BoujeeEnjinia1701/floodgauge/cad/drawings/FLG-DWG-001.pdf

CONCEPT, NOT FOR FABRICATION | FloodGauge · github.com/BoujeeEnjinia1701/floodgauge

TOP VIEW
Scale 1:50; looking down (along -Z)

FRONT VIEW
Scale 1:50; looking along the street

RIGHT VIEW
Scale 1:50; looking at the right side (along -X)

DETAIL A: STREET HEAD, ARM AND CLAMPS
Scale 1:10; front view

SECTION B: CATCH BASIN, DRAIN HEAD AND TUBE
Scale 1:20; basin cut on the street axis

PRELIMINARY, NOT FOR FABRICATION

ROAD, Z = 0 (DATUM)

SIDEWALK

4,600 lens to road

3,400 node center

300

250

CURB FACE

715 arm
700 head to pole axis

400 clamps

2 RADAR HEAD D76

M8 THROUGH-BOLT, ANTI-ROTATION

POLE BRACKET PLATE ON 2 V-BLOCKS

3 ARM 40 x 40 x 1.6

KNEE BRACE 25 SQ, 45 DEG

300
330

1,240 mouth

ROAD Z = 0

5 TUBE 75 OD x 940

4 DRAIN HEAD

WATER ENTERS VIA SLOTS

ISOMETRIC VIEW
Kit on the existing pole; not to scale; seen from the front right and above, about 30 deg elevation

MAIN DIMENSIONS AND INTERFACES (MM)
Datum: road surface at the gauge point, Z = 0; curb 150 Radar lens 4,600 above road, 250 past curb face Street depth 0 to 600: range 4,600 to 4,000
FieldNode 150 x 90 x 200 on 60 pole, center 3,400 Arm 40 sq x 715 in cleats on a 3 x 100 x 450 plate Pole bracket on 2 V-blocks, band clamps 400 apart
Tube 75 OD, ID 69, 940 long, 40 slots 5 x 50
Drain reading 330 to 1,250 below road; probe 310
Pilot cable route: 3 hat covers 764 long, curb and sidewalk anchors; riser guard Marker bands 150 to 300 amber, 300 to 450 red
Lens height 2,500 to 5,000 per site, clearance rule (FLG-CAL-001 A7)
REV | DESCRIPTION | DATE | BY
P1 | Preliminary GA for TRL 3 (from cad/src/model.py) | 2026-09-25 | AC
P2 | DDR-002: lens 4.6 m, node 3.0 m, surface cable cover, anti-rotation bolt | 2026-09-25 | AC
P3 | Layout and labels tidied | 2026-09-25 | AC
P4 | DDR-003: constructable design; node at 3.4 m | 2026-10-01 | AC
P5 | Drain cable slack loop tied to tube clamp | 2026-10-02 | AC
FLOODGAUGE | github.com/BoujeeEnjinia1701/floodgauge

## General arrangement

DRAWING NO.
FLG-DWG-001

REV
P5

SHEET
1 of 1

SIZE

## ANSI B

SCALE
1:50

UNITS
mm
PROJECTION | DATE
2026-10-02

DRAWN
Amish Chadha

MATERIAL / NOTES
Aluminium arm, PVC tube, bought-in heads per bom/bom.csv; existing street shown for context. PRELIMINARY, NOT FOR FABRICATION
Licensed CERN-OHL-S-2.0 · Design Molecule Lab · designmolecule.com | Generated from cad/src; do not edit by hand
