BoujeeEnjinia1701/floodgauge/cad/drawings/FLG-DWG-110.pdf

BUILD PLAN SKETCH, PLAN NOT YET BUILT FloodGauge · github.com/BoujeeEnjinia1701/floodgauge

FRONT VIEW
Scale 1:5; looking at the front (along +Y)

TOP VIEW
Scale 1:5; looking down (along -Z)

RIGHT VIEW
Scale 1:5; looking at the right side (along -X)

90

2 435

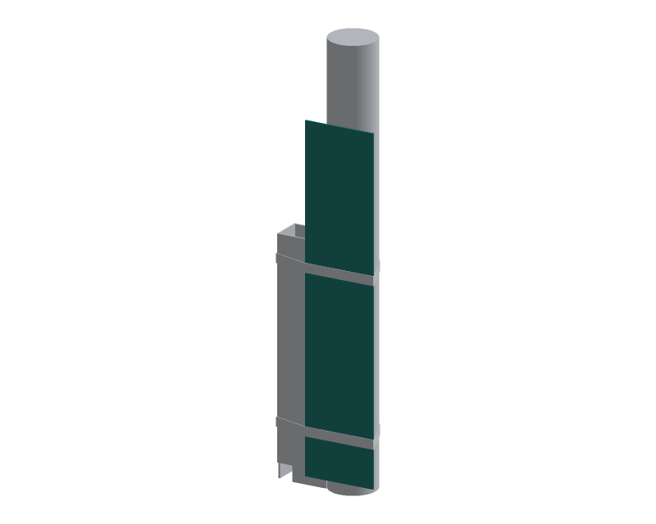
[picture p8: figure]

WHERE IT GOES
This part in colour, its neighbours in grey

HOW TO MAKE IT AND HOW IT FITS
Cut 90 x 435 mm from 2 mm aluminium; round the corners, deburr.
The bottom edge sits 165 mm above the road (15 mm above the sidewalk), so the sidewalk cover passes under it. Heights below are from the road.
Amber reflective film from the bottom edge up to 300 mm above the road (135 mm up the plate). Red film from 300 to 450 mm above the road
(135 to 285 mm up the plate). Leave the top 150 mm plain for a label. Mark a black line at 150 mm and 300 mm above the road (the alert depths) and number them.
No holes: two band clamps go round the pole, across the plate's face and round the riser guard, at 220 and 420 mm above the road. Check: film edges straight and level when the plate is held plumb.
REV | DESCRIPTION | DATE | BY
P1 | Making sketch for the prototype build plan | 2026-10-01 | AC
FLOODGAUGE | github.com/BoujeeEnjinia1701/floodgauge

## FloodGauge depth marker plate: making sketch

DRAWING NO.
FLG-DWG-110

REV
P1

SHEET
1 of 1

SIZE

## ANSI B

SCALE
1:5

UNITS
mm
PROJECTION | DATE
2026-10-01

DRAWN
Amish Chadha

MATERIAL / NOTES
Aluminium sheet 2 mm with reflective film
Licensed CERN-OHL-S-2.0 · Design Molecule Lab · designmolecule.com | Generated from cad/src; do not edit by hand
