BoujeeEnjinia1701/floodgauge/cad/drawings/FLG-DWG-111.pdf

BUILD PLAN SKETCH, PLAN NOT YET BUILT FloodGauge · github.com/BoujeeEnjinia1701/floodgauge

FRONT VIEW
Scale 1:5; looking at the front (along +Y)

TOP VIEW
Scale 1:5; looking down (along -Z)

RIGHT VIEW
Scale 1:5; looking at the right side (along -X)

40

65 300

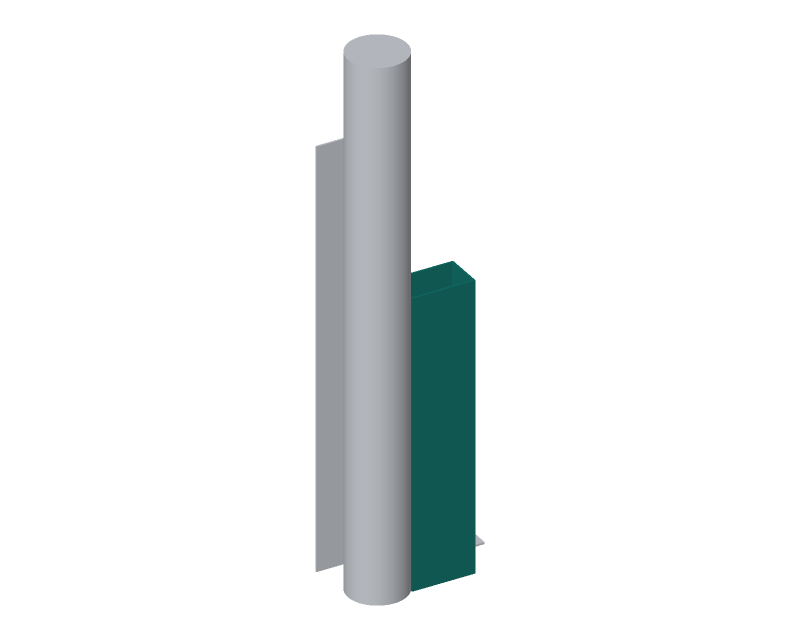
[picture p9: figure]

WHERE IT GOES
This part in colour, its neighbours in grey

HOW TO MAKE IT AND HOW IT FITS
Cut a blank 300 x 162 mm from 2 mm galvanized sheet.
Fold to a U: back 40 mm wide outside, two sides 65 mm deep. Fold in a sheet folder or over a hardwood block in the vice.
Cut a 20 x 20 mm notch at the foot of the side that faces the road, against the back: the cable comes out of the sidewalk cover here. File every edge smooth; paint the cut edges with zinc paint.
Fit: open side against the pole, the free edges of both sides bearing
on the pole; it stands on the sidewalk beside the pole, 300 mm tall.
The two marker band clamps go round it and hold it (pin-Torx security screws). Check: the free edges touch the pole along their whole length.
REV | DESCRIPTION | DATE | BY
P1 | Making sketch for the prototype build plan | 2026-10-01 | AC
FLOODGAUGE | github.com/BoujeeEnjinia1701/floodgauge

## FloodGauge riser guard: making sketch

DRAWING NO.
FLG-DWG-111

REV
P1

SHEET
1 of 1

SIZE

## ANSI B

SCALE
1:5

UNITS
mm
PROJECTION | DATE
2026-10-01

DRAWN
Amish Chadha

MATERIAL / NOTES
Galvanized steel sheet 2 mm
Licensed CERN-OHL-S-2.0 · Design Molecule Lab · designmolecule.com | Generated from cad/src; do not edit by hand
