BoujeeEnjinia1701/floodgauge/cad/drawings/FLG-DWG-114.pdf

BUILD PLAN SKETCH, PLAN NOT YET BUILT FloodGauge · github.com/BoujeeEnjinia1701/floodgauge

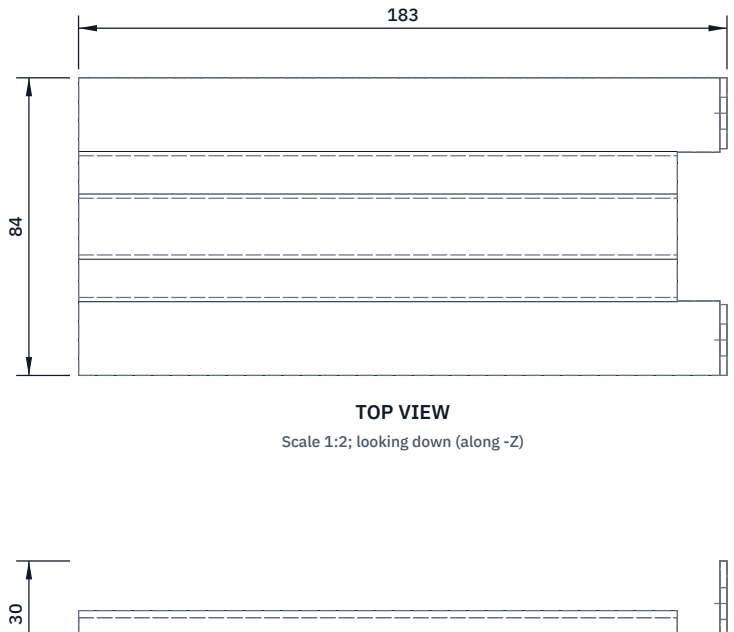
[picture p10: figure]
TOP VIEW; Scale 1:2; looking down (along -Z)

FRONT VIEW
Scale 1:2; looking at the front (along +Y)

RIGHT VIEW
Scale 1:2; looking at the right side (along -X)

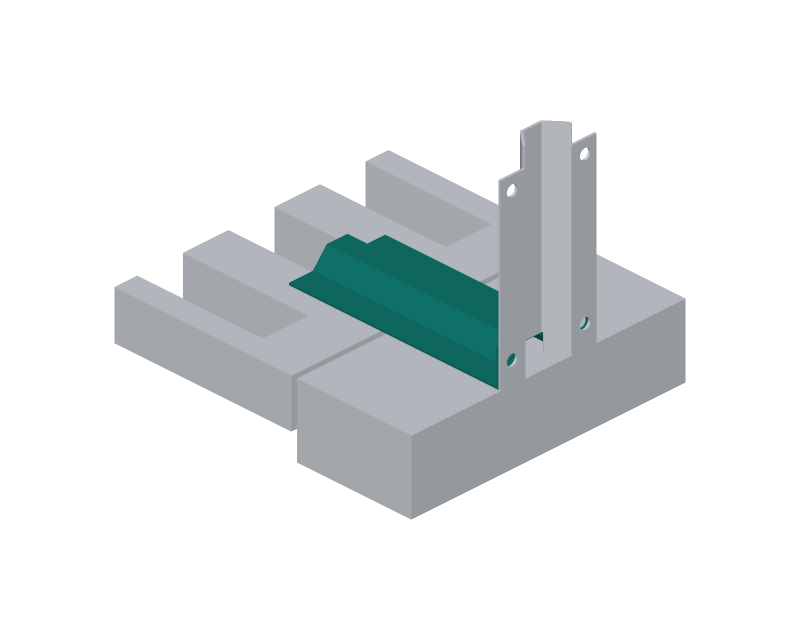
[picture p11: figure]

WHERE IT GOES
This part in colour, its neighbours in grey

HOW TO MAKE IT AND HOW IT FITS
Hat section: from 2 mm galvanized strip 84 mm wide, folded to two
22 mm flanges, two 45 degree sides and a 16 mm wide top, 16 mm high overall. Fold in a sheet folder; cut lengths with a grinder.
Paint the cut ends with zinc paint; file all edges smooth.
Cut 211 mm of hat section. At one end cut away the top and
sides for 42 mm, leaving the two flanges; fold the flanges up
90 degrees 30 mm from their ends to make the tabs (169 mm of raised part). Drill a 9 mm hole in each tab, 18 mm up, 32 mm from the centre line.
Fit: lies across the gutter strip and 80 mm onto the grate's border,
over the cable. The tabs go over the curb cover's flanges and
share its two lower anchors (security nuts). Nothing is fixed to the road. Check: lies flat with no rocking.
REV | DESCRIPTION | DATE | BY
P1 | Making sketch for the prototype build plan | 2026-10-01 | AC
FLOODGAUGE | github.com/BoujeeEnjinia1701/floodgauge

## FloodGauge gutter cover: making sketch

DRAWING NO.
FLG-DWG-114

REV
P1

SHEET
1 of 1

SIZE

## ANSI B

SCALE
1:2

UNITS
mm
PROJECTION | DATE
2026-10-01

DRAWN
Amish Chadha

MATERIAL / NOTES
Galvanized steel strip 2 mm
Licensed CERN-OHL-S-2.0 · Design Molecule Lab · designmolecule.com | Generated from cad/src; do not edit by hand
