BoujeeEnjinia1701/floodgauge/cad/drawings/FLG-DWG-115.pdf

BUILD PLAN SKETCH, PLAN NOT YET BUILT FloodGauge · github.com/BoujeeEnjinia1701/floodgauge

FRONT VIEW
Scale 1:2; looking at the front (along +Y)

TOP VIEW
Scale 1:2; looking down (along -Z)

RIGHT VIEW
Scale 1:2; looking at the right side (along -X)

16

84 166

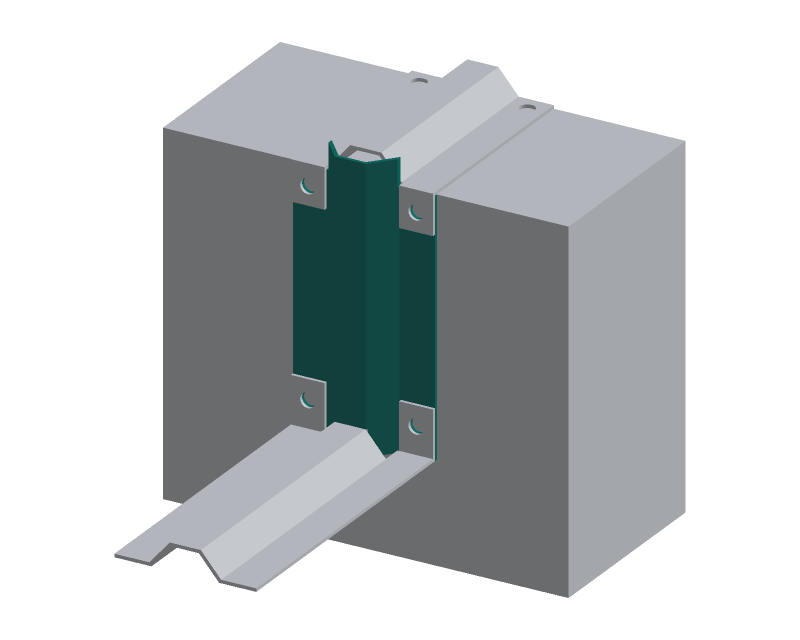
[picture p12: figure]

WHERE IT GOES
This part in colour, its neighbours in grey

HOW TO MAKE IT AND HOW IT FITS
Hat section: from 2 mm galvanized strip 84 mm wide, folded to two
22 mm flanges, two 45 degree sides and a 16 mm wide top, 16 mm high overall. Fold in a sheet folder; cut lengths with a grinder.
Paint the cut ends with zinc paint; file all edges smooth.
Length 166 mm of hat section. Cut both flanges off the top 16 mm (only the raised part rises above the sidewalk).
Cut a 20 x 16 mm notch in the raised face at the bottom end for the cable coming out of the gutter cover.
Four 9 mm holes in the flanges, 32 mm from the centre line, 18 and 139 mm up from the bottom end.
Fit: flanges flat on the curb face, standing on the road; four M8 masonry anchors, snake-eye security nuts, through it and the tabs. Check: the top of the raised part is 16 mm above the sidewalk.
REV | DESCRIPTION | DATE | BY
P1 | Making sketch for the prototype build plan | 2026-10-01 | AC
FLOODGAUGE | github.com/BoujeeEnjinia1701/floodgauge

## FloodGauge curb cover: making sketch

DRAWING NO.
FLG-DWG-115

REV
P1

SHEET
1 of 1

SIZE

## ANSI B

SCALE
1:2

UNITS
mm
PROJECTION | DATE
2026-10-01

DRAWN
Amish Chadha

MATERIAL / NOTES
Galvanized steel strip 2 mm
Licensed CERN-OHL-S-2.0 · Design Molecule Lab · designmolecule.com | Generated from cad/src; do not edit by hand
