BoujeeEnjinia1701/floodgauge/cad/drawings/FLG-DWG-116.pdf

BUILD PLAN SKETCH, PLAN NOT YET BUILT FloodGauge · github.com/BoujeeEnjinia1701/floodgauge

FRONT VIEW
Scale 1:5; looking at the front (along +Y)

TOP VIEW
Scale 1:5; looking down (along -Z)

RIGHT VIEW
Scale 1:5; looking at the right side (along -X)

433

84 38

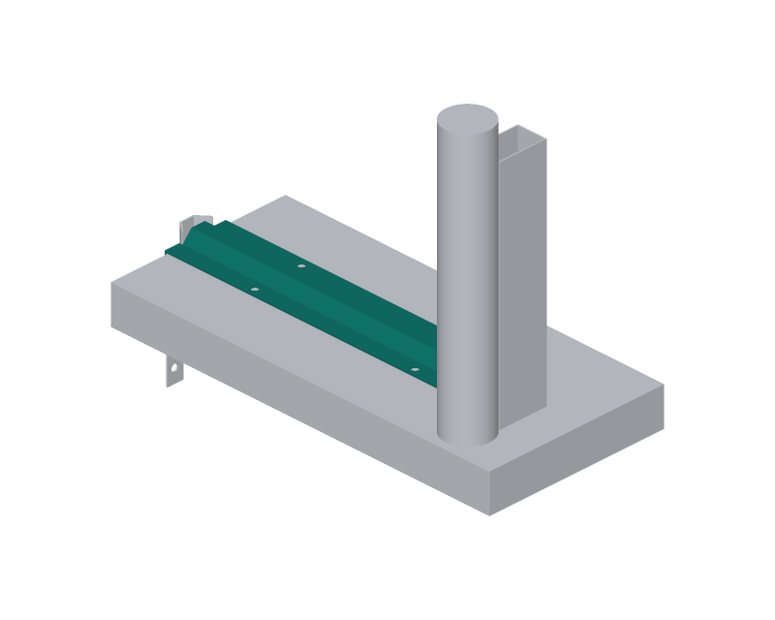
[picture p13: figure]

WHERE IT GOES
This part in colour, its neighbours in grey

HOW TO MAKE IT AND HOW IT FITS
Hat section: from 2 mm galvanized strip 84 mm wide, folded to two
22 mm flanges, two 45 degree sides and a 16 mm wide top, 16 mm high overall. Fold in a sheet folder; cut lengths with a grinder.
Paint the cut ends with zinc paint; file all edges smooth.
Cut 455 mm of hat section. At one end cut away the top and
sides for 26 mm, leaving the two flanges; fold the flanges down
90 degrees 22 mm from their ends to make the tabs (429 mm raised). Four 9 mm holes in the flanges, 32 mm from the centre line, 110 and 330 mm from the curb end; a 9 mm hole in each tab, 11 mm down. Grind a 45 degree bevel on the flange edges so it is not a trip edge. Fit: across the sidewalk from the curb edge to 1 mm short of the riser guard; four M8 anchors, security nuts; tabs share the curb cover's upper anchors. Paint it yellow or fit hazard tape.
Check: no edge stands more than 2 mm off the sidewalk.
REV | DESCRIPTION | DATE | BY
P1 | Making sketch for the prototype build plan | 2026-10-01 | AC
FLOODGAUGE | github.com/BoujeeEnjinia1701/floodgauge

## FloodGauge sidewalk cover: making sketch

DRAWING NO.
FLG-DWG-116

REV
P1

SHEET
1 of 1

SIZE

## ANSI B

SCALE
1:5

UNITS
mm
PROJECTION | DATE
2026-10-01

DRAWN
Amish Chadha

MATERIAL / NOTES
Galvanized steel strip 2 mm
Licensed CERN-OHL-S-2.0 · Design Molecule Lab · designmolecule.com | Generated from cad/src; do not edit by hand
