BoujeeEnjinia1701/floodgauge/cad/drawings/FLG-DWG-101.pdf

BUILD PLAN SKETCH, PLAN NOT YET BUILT FloodGauge · github.com/BoujeeEnjinia1701/floodgauge

FRONT VIEW
Scale 1:5; looking at the front (along +Y)

TOP VIEW
Scale 1:5; looking down (along -Z)

RIGHT VIEW
Scale 1:5; looking at the right side (along -X)

100

3 450

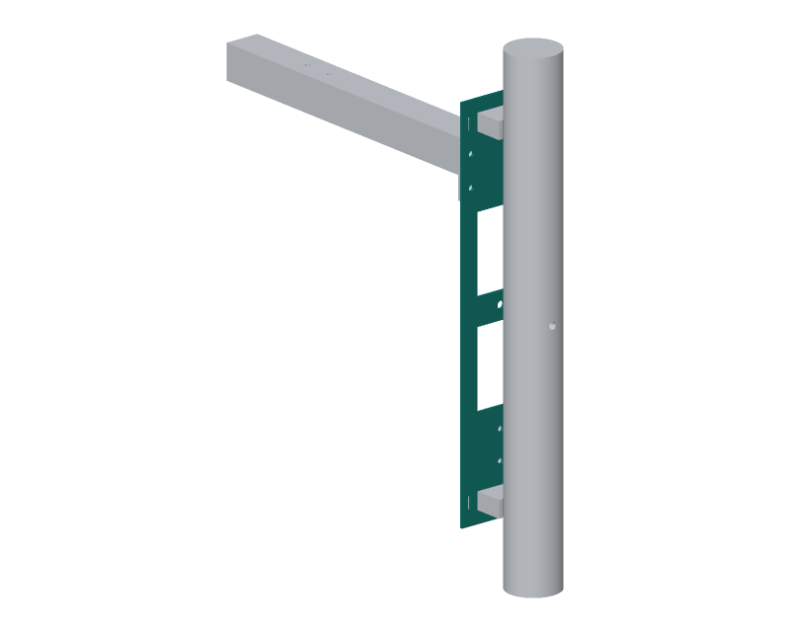
[picture p53: figure]

WHERE IT GOES
This part in colour, its neighbours in grey

HOW TO MAKE IT AND HOW IT FITS
Blank 100 x 450 mm, 3 mm aluminium. Front view is the face toward the road. Heights up from the bottom edge; sideways from the centre line.
Band slots 3 x 15 mm at 40 mm each side, centred 25 and 425 mm up:
chain drill 3 mm and file square. The band clamps pass through these. V-block screws 4.5 mm at 18 mm each side, 25 and 425 mm up; countersink from the front so the M4 heads sit flush under the band.
Brace clip bolts 6.6 mm on the centre line, 60 and 94 mm up.
Through-bolt hole 8.5 mm on the centre line, 225 mm up.
Arm cleat bolts 6.6 mm at 38 mm each side, 357 and 393 mm up.
Two windows 60 x 90 mm, centred 164 and 285 mm up (saves weight): drill 10 mm in the corners, cut between with a jigsaw, file straight. Deburr every hole and edge; round the corners to about 2 mm.
Check: lay the V-blocks, cleats and clip on it; every hole lines up.
REV | DESCRIPTION | DATE | BY
P1 | Making sketch for the prototype build plan | 2026-10-01 | AC
FLOODGAUGE | github.com/BoujeeEnjinia1701/floodgauge

## FloodGauge pole bracket plate: making sketch

DRAWING NO.
FLG-DWG-101

REV
P1

SHEET
1 of 1

SIZE

## ANSI B

SCALE
1:5

UNITS
mm
PROJECTION | DATE
2026-10-01

DRAWN
Amish Chadha

MATERIAL / NOTES
Aluminium sheet 3 mm, 5052 or 6061 class
Licensed CERN-OHL-S-2.0 · Design Molecule Lab · designmolecule.com | Generated from cad/src; do not edit by hand
