BoujeeEnjinia1701/floodgauge/cad/drawings/FLG-DWG-102.pdf

BUILD PLAN SKETCH, PLAN NOT YET BUILT FloodGauge · github.com/BoujeeEnjinia1701/floodgauge

FRONT VIEW
Scale 1:1; looking at the front (along +Y)

TOP VIEW
Scale 1:1; looking down (along -Z)

RIGHT VIEW
Scale 1:1; looking at the right side (along -X)

33

60 20

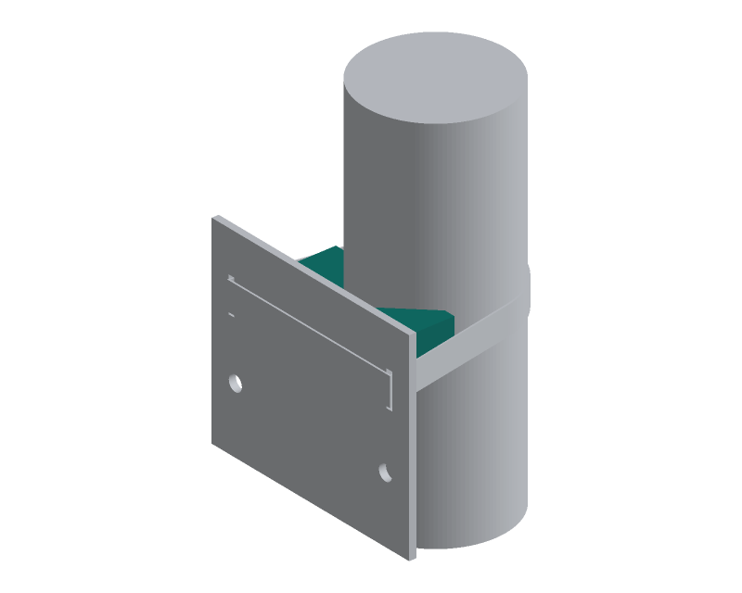
[picture p54: figure]

WHERE IT GOES
This part in colour, its neighbours in grey

HOW TO MAKE IT AND HOW IT FITS
Make two; the same block as FieldNode's (FND-DWG-102). Saw a 20 mm slice off 60 x 40 mm bar; saw and file to 60 wide x 33 deep x 20 tall.
The flat back goes on the bracket plate.
Scribe a 90 degree V on both 60 x 33 faces with a 45 degree square: 50.4 mm wide at the front face, point 7.8 mm from the back face. Saw just inside the lines, file to them; keep the V faces flat.
Break the V's front edges 0.5 mm so they cannot score the pole. Drill 3.3 mm 14 deep and tap M4 12 deep in the back face, at 18 mm each side of centre, half way up (10 mm).
Fit: two M4 countersunk screws from the front of the plate. The 60 mm pole touches both V faces 29 mm from the plate; 40 to 71 mm poles seat. Check: on a 60 mm tube the block must not rock.
REV | DESCRIPTION | DATE | BY
P1 | Making sketch for the prototype build plan | 2026-10-01 | AC
FLOODGAUGE | github.com/BoujeeEnjinia1701/floodgauge

## FloodGauge V-block (make 2): making sketch

DRAWING NO.
FLG-DWG-102

REV
P1

SHEET
1 of 1

SIZE

## ANSI B

SCALE
1:1

UNITS
mm
PROJECTION | DATE
2026-10-01

DRAWN
Amish Chadha

MATERIAL / NOTES
Aluminium flat bar 60 x 40 mm, 6082 or 6061
Licensed CERN-OHL-S-2.0 · Design Molecule Lab · designmolecule.com | Generated from cad/src; do not edit by hand
