BoujeeEnjinia1701/floodgauge/cad/drawings/FLG-DWG-103.pdf

BUILD PLAN SKETCH, PLAN NOT YET BUILT FloodGauge · github.com/BoujeeEnjinia1701/floodgauge

FRONT VIEW
Scale 1:1; looking at the front (along +Y)

TOP VIEW
Scale 1:1; looking down (along -Z)

RIGHT VIEW
Scale 1:1; looking at the right side (along -X)

30

30 60

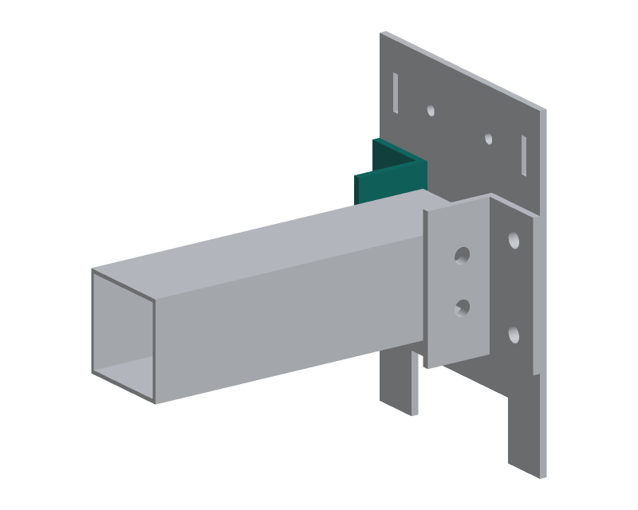
[picture p55: figure]

WHERE IT GOES
This part in colour, its neighbours in grey

HOW TO MAKE IT AND HOW IT FITS
Cut two 60 mm lengths of 30 x 30 x 3 angle; square and deburr the ends. Plate leg (goes flat on the bracket plate): two 6.6 mm holes, 12 mm
in from its free edge, 12 and 48 mm up from the bottom end.
Arm leg (lies along the arm's side): two 6.6 mm holes, 15 mm out from the face that sits on the plate, 20 and 40 mm up from the bottom end. Left and right cleats are mirror images: drill them clamped as a pair. Fit: plate legs flat on the plate front, 345 to 405 mm up it, arm legs 40 mm apart; two M6 bolts each through the plate (nuts behind);
the arm slides between the arm legs and two M6 bolts with crush sleeves pass through cleat, arm and cleat.
Check: both cleats square to the plate, arm legs parallel, 40 mm apart.
REV | DESCRIPTION | DATE | BY
P1 | Making sketch for the prototype build plan | 2026-10-01 | AC
FLOODGAUGE | github.com/BoujeeEnjinia1701/floodgauge

## FloodGauge arm cleat (make 2, a left and a right): making sketch

DRAWING NO.
FLG-DWG-103

REV
P1

SHEET
1 of 1

SIZE

## ANSI B

SCALE
1:1

UNITS
mm
PROJECTION | DATE
2026-10-01

DRAWN
Amish Chadha

MATERIAL / NOTES
Aluminium equal angle 30 x 30 x 3 mm
Licensed CERN-OHL-S-2.0 · Design Molecule Lab · designmolecule.com | Generated from cad/src; do not edit by hand
