BoujeeEnjinia1701/floodgauge/cad/drawings/FLG-DWG-104.pdf

BUILD PLAN SKETCH, PLAN NOT YET BUILT FloodGauge · github.com/BoujeeEnjinia1701/floodgauge

FRONT VIEW
Scale 1:1; looking at the front (along +Y)

TOP VIEW
Scale 1:1; looking down (along -Z)

RIGHT VIEW
Scale 1:1; looking at the right side (along -X)

32

32 50

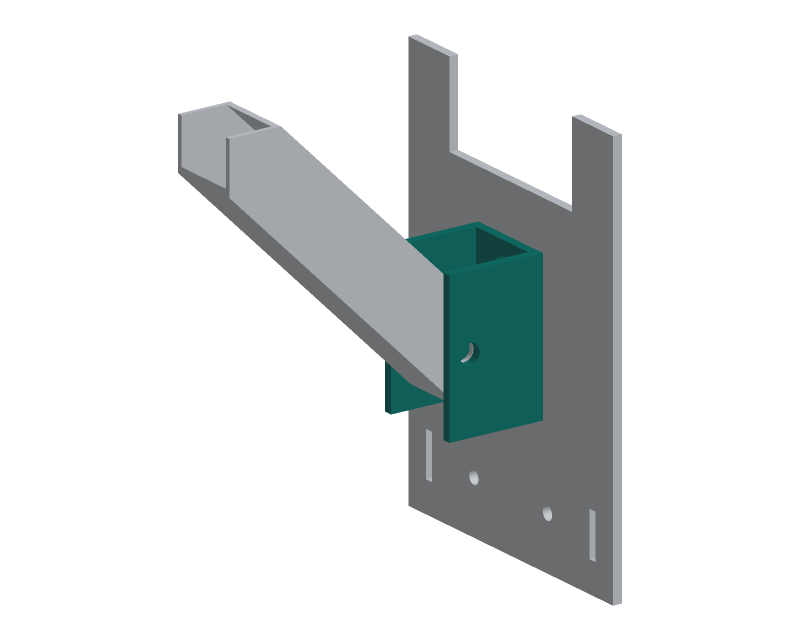
[picture p56: figure]

WHERE IT GOES
This part in colour, its neighbours in grey

HOW TO MAKE IT AND HOW IT FITS
Make two the same. Cut a 50 x 90 mm blank from 3 mm strip. Fold it to a U: base 31.5 mm wide outside, inside gap 25.5 mm,
ears 32 mm deep from the outside of the base. Fold in a vice over
a 25 mm steel block so the gap comes out right.
Base: two 6.6 mm holes on the centre line, 17 mm each side of the middle. Ears: one 6.6 mm hole through both, at mid-length, 25 mm out from
the outside of the base. Drill both ears in one pass after folding.
Fit: one clip under the arm, base up, ears hanging down (two M6 bolts
up through the arm, crush sleeves, nuts on top). The other on the bracket plate, ears forward (two M6 bolts, nuts behind the plate). The brace end sits between the ears on one M6 pin with a sleeve. Check: a 25 mm square tube slides between the ears without play.
REV | DESCRIPTION | DATE | BY
P1 | Making sketch for the prototype build plan | 2026-10-01 | AC
FLOODGAUGE | github.com/BoujeeEnjinia1701/floodgauge

## FloodGauge brace clip (make 2): making sketch

DRAWING NO.
FLG-DWG-104

REV
P1

SHEET
1 of 1

SIZE

## ANSI B

SCALE
1:1

UNITS
mm
PROJECTION | DATE
2026-10-01

DRAWN
Amish Chadha

MATERIAL / NOTES
Aluminium strip 3 mm x 50 mm, 5052 class
Licensed CERN-OHL-S-2.0 · Design Molecule Lab · designmolecule.com | Generated from cad/src; do not edit by hand
