BoujeeEnjinia1701/floodgauge/cad/drawings/FLG-DWG-105.pdf

BUILD PLAN SKETCH, PLAN NOT YET BUILT FloodGauge · github.com/BoujeeEnjinia1701/floodgauge

FRONT VIEW
Scale 1:5; looking at the front (along +Y)

TOP VIEW
Scale 1:5; looking down (along -Z)

RIGHT VIEW
Scale 1:5; looking at the right side (along -X)

715

40 40

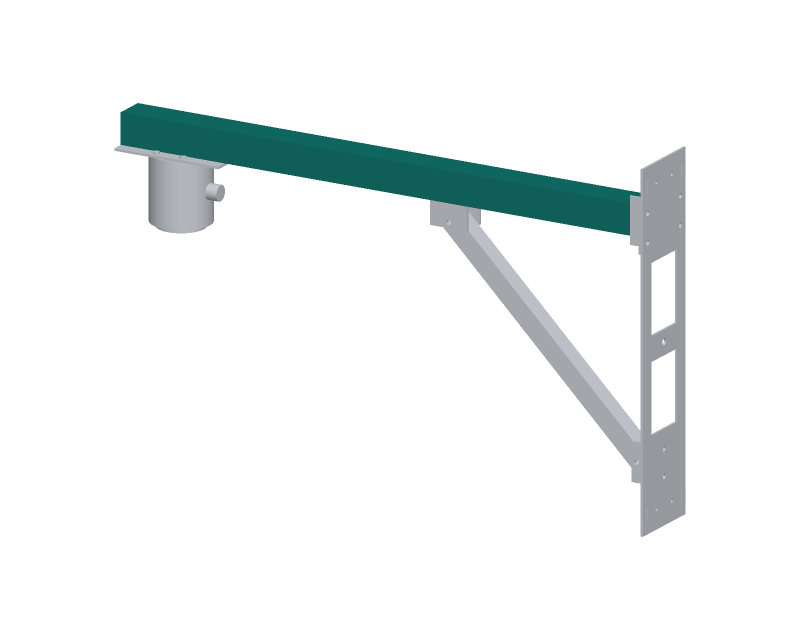
[picture p57: figure]

WHERE IT GOES
This part in colour, its neighbours in grey

HOW TO MAKE IT AND HOW IT FITS
Cut 715 mm of 40 x 40 x 1.6 tube; square and deburr both ends.
Measure from the pole end (the end that goes between the cleats). Cleat bolts: two 6.6 mm holes across the side faces, 13 mm from the pole end, 10 mm above and below the centre line. Drill through both sides. Brace clip bolts: two 6.6 mm holes down through top and bottom, on the centre line, 259 and 293 mm from the pole end.
Head plate bolts: two 6.6 mm holes down through top and bottom, on the centre line, 590 and 700 mm from the pole end.
Use a drill stand so every hole goes square through both walls.
Fit a 6 mm aluminium crush sleeve inside at every bolt so the tube
walls are not squeezed in; push a plastic cap into the road end. The radar head axis is 700 mm from the pole axis.
Check: lay it on the bench; the hole rows line up along the centre.
REV | DESCRIPTION | DATE | BY
P1 | Making sketch for the prototype build plan | 2026-10-01 | AC
FLOODGAUGE | github.com/BoujeeEnjinia1701/floodgauge

## FloodGauge sensor arm: making sketch

DRAWING NO.
FLG-DWG-105

REV
P1

SHEET
1 of 1

SIZE

## ANSI B

SCALE
1:5

UNITS
mm
PROJECTION | DATE
2026-10-01

DRAWN
Amish Chadha

MATERIAL / NOTES
Aluminium square tube 40 x 40 x 1.6 mm, 6063-T6
Licensed CERN-OHL-S-2.0 · Design Molecule Lab · designmolecule.com | Generated from cad/src; do not edit by hand
