BoujeeEnjinia1701/floodgauge/cad/drawings/FLG-DWG-106.pdf

BUILD PLAN SKETCH, PLAN NOT YET BUILT FloodGauge · github.com/BoujeeEnjinia1701/floodgauge

FRONT VIEW
Scale 1:2; looking at the front (along +Y)

TOP VIEW
Scale 1:2; looking down (along -Z)

RIGHT VIEW
Scale 1:2; looking at the right side (along -X)

382

25 25

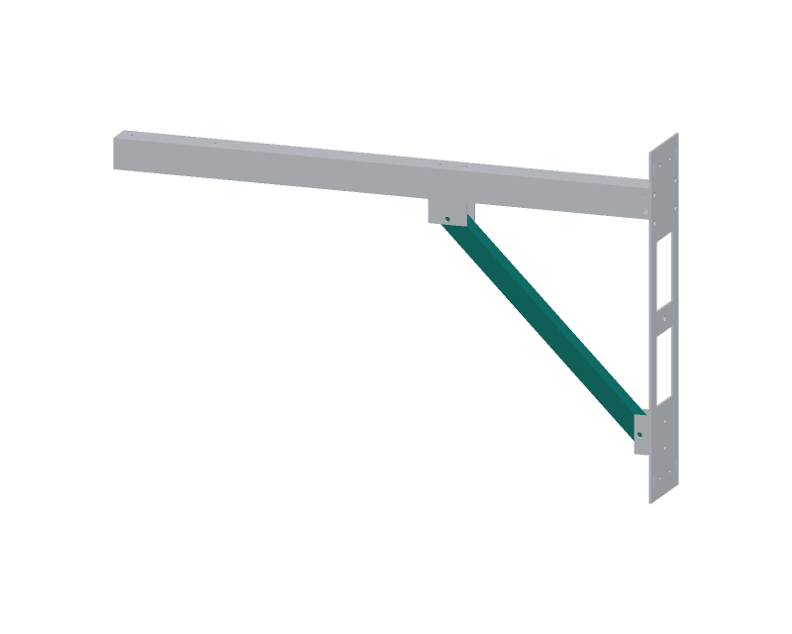
[picture p58: figure]

WHERE IT GOES
This part in colour, its neighbours in grey

HOW TO MAKE IT AND HOW IT FITS
Cut 382 mm of 25 x 25 x 1.6 tube; cut both ends square, deburr. Drill a 6.6 mm hole across through both walls 12 mm from each end: the two holes are 357.8 mm apart. Drill with the tube flat in a vice. Fit a 6 mm aluminium crush sleeve (21.8 mm long) at each hole. Fit: the brace runs at 45 degrees from the clip on the bracket plate up to the clip under the arm (253 mm up and 253 mm out),
on one M6 pin at each end. It holds the arm level and takes the load of anything hanging on the head.
Check: hole centres within 0.5 mm; with the arm level, both pins slide in by hand.
REV | DESCRIPTION | DATE | BY
P1 | Making sketch for the prototype build plan | 2026-10-01 | AC
FLOODGAUGE | github.com/BoujeeEnjinia1701/floodgauge

## FloodGauge knee brace: making sketch

DRAWING NO.
FLG-DWG-106

REV
P1

SHEET
1 of 1

SIZE

## ANSI B

SCALE
1:2

UNITS
mm
PROJECTION | DATE
2026-10-01

DRAWN
Amish Chadha

MATERIAL / NOTES
Aluminium square tube 25 x 25 x 1.6 mm, 6063-T6
Licensed CERN-OHL-S-2.0 · Design Molecule Lab · designmolecule.com | Generated from cad/src; do not edit by hand
