BoujeeEnjinia1701/floodgauge/cad/drawings/FLG-DWG-107.pdf

BUILD PLAN SKETCH, PLAN NOT YET BUILT FloodGauge · github.com/BoujeeEnjinia1701/floodgauge

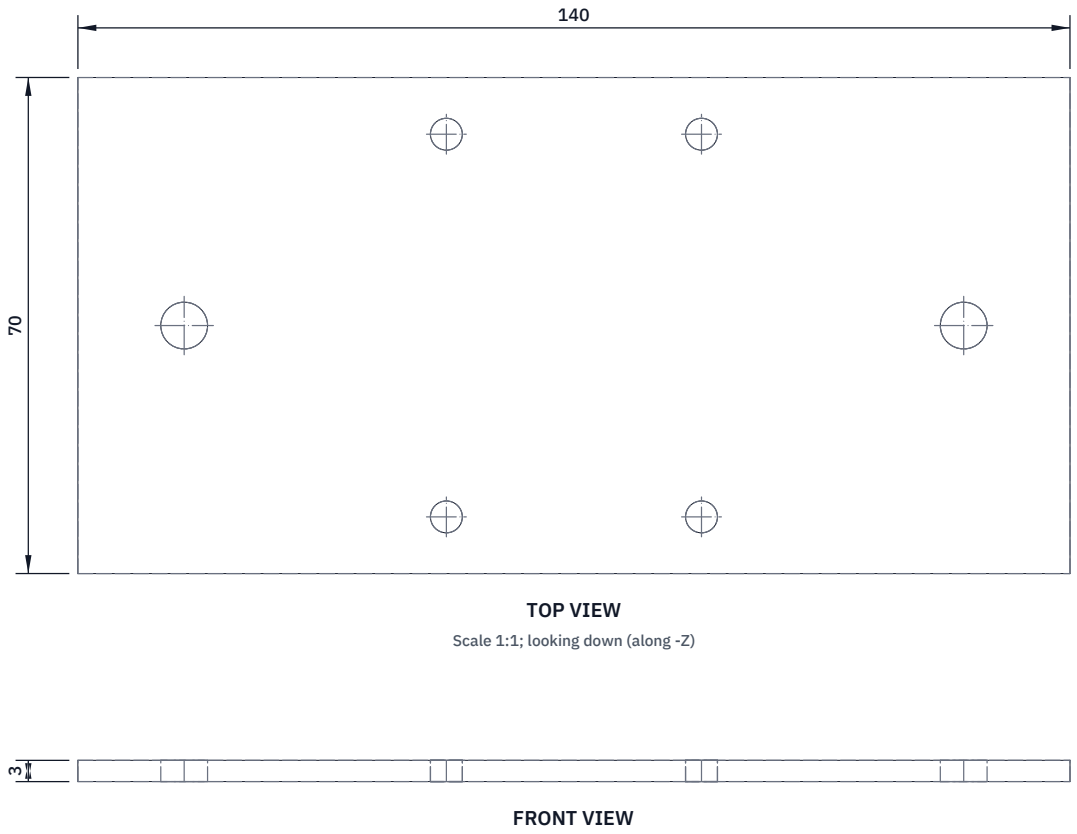
[picture p59: figure]
FRONT VIEW; TOP VIEW; Scale 1:1; looking down (along -Z)

Scale 1:1; looking at the front (along +Y)

RIGHT VIEW
Scale 1:1; looking at the right side (along -X)

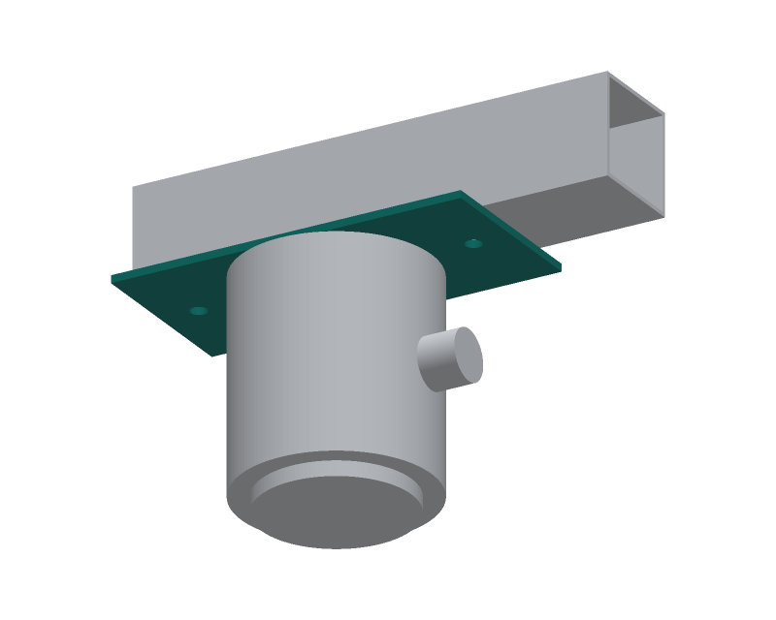
[picture p60: figure]

WHERE IT GOES
This part in colour, its neighbours in grey

HOW TO MAKE IT AND HOW IT FITS
Cut 140 x 70 mm from 3 mm sheet; round the corners, deburr.
Two 6.6 mm holes on the long centre line, 55 mm each side of the middle (they line up with the head plate holes in the arm).
Four 4.5 mm holes, countersunk on the top face, 18 mm each side of the middle along the plate and 27 mm each side across it.
Check the radar housing's lid bosses before drilling and move these four holes to suit the housing you buy.
Fit: under the arm, long side along it, centred on the head axis;
two M6 bolts up through plate and arm, crush sleeves, nuts on top. The housing hangs below on four M4 countersunk screws.
Check: plate flat; the housing sits square under it.
REV | DESCRIPTION | DATE | BY
P1 | Making sketch for the prototype build plan | 2026-10-01 | AC
FLOODGAUGE | github.com/BoujeeEnjinia1701/floodgauge

## FloodGauge head plate: making sketch

DRAWING NO.
FLG-DWG-107

REV
P1

SHEET
1 of 1

SIZE

## ANSI B

SCALE
1:1

UNITS
mm
PROJECTION | DATE
2026-10-01

DRAWN
Amish Chadha

MATERIAL / NOTES
Aluminium sheet 3 mm, 5052 or 6061 class
Licensed CERN-OHL-S-2.0 · Design Molecule Lab · designmolecule.com | Generated from cad/src; do not edit by hand
