BoujeeEnjinia1701/floodgauge/cad/drawings/FLG-DWG-108.pdf

BUILD PLAN SKETCH, PLAN NOT YET BUILT FloodGauge · github.com/BoujeeEnjinia1701/floodgauge

FRONT VIEW
Scale 1:2; looking at the front (along +Y)

TOP VIEW
Scale 1:2; looking down (along -Z)

RIGHT VIEW
Scale 1:2; looking at the right side (along -X)

91

76 90

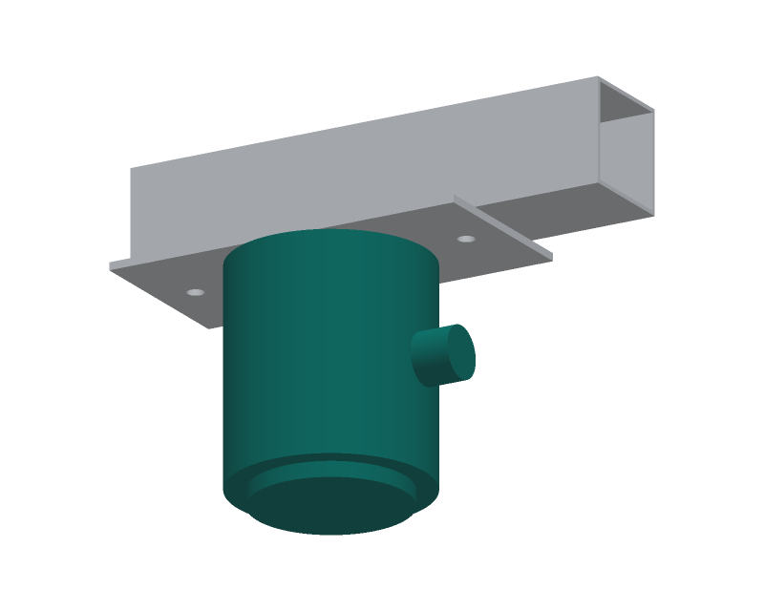
[picture p61: figure]

WHERE IT GOES
This part in colour, its neighbours in grey

HOW TO MAKE IT AND HOW IT FITS
Housing: a round IP67 box about 76 mm across and 84 mm tall, with a base that can be drilled and four lid bosses on top.
Drill a 46 mm window in the centre of the base (hole saw, slow). Lens: a 60 x 6 mm PTFE disc (cut from rod or bought). Bed it on neutral-cure silicone over the window outside the base and hold it with three M3 stainless screws on a 53 mm circle.
Drill an M12 gland hole in the side, half way up, facing the pole. Mount the radar module on its carrier on four standoffs inside the base, its antenna face centred over the window.
Fit: the housing top screws to the head plate (four M4 countersunk).
The underside of the lens is the datum: 4,600 mm above the road. Check: lens flat and square to the housing; gland seals on a 10 mm cable.
REV | DESCRIPTION | DATE | BY
P1 | Making sketch for the prototype build plan | 2026-10-01 | AC
FLOODGAUGE | github.com/BoujeeEnjinia1701/floodgauge

## FloodGauge street radar head: making sketch

DRAWING NO.
FLG-DWG-108

REV
P1

SHEET
1 of 1

SIZE

## ANSI B

SCALE
1:2

UNITS
mm
PROJECTION | DATE
2026-10-01

DRAWN
Amish Chadha

MATERIAL / NOTES
Bought IP67 round housing 76 mm; PTFE disc 60 x 6 mm
Licensed CERN-OHL-S-2.0 · Design Molecule Lab · designmolecule.com | Generated from cad/src; do not edit by hand
