BoujeeEnjinia1701/floodgauge/cad/drawings/FLG-DWG-109.pdf

BUILD PLAN SKETCH, PLAN NOT YET BUILT FloodGauge · github.com/BoujeeEnjinia1701/floodgauge

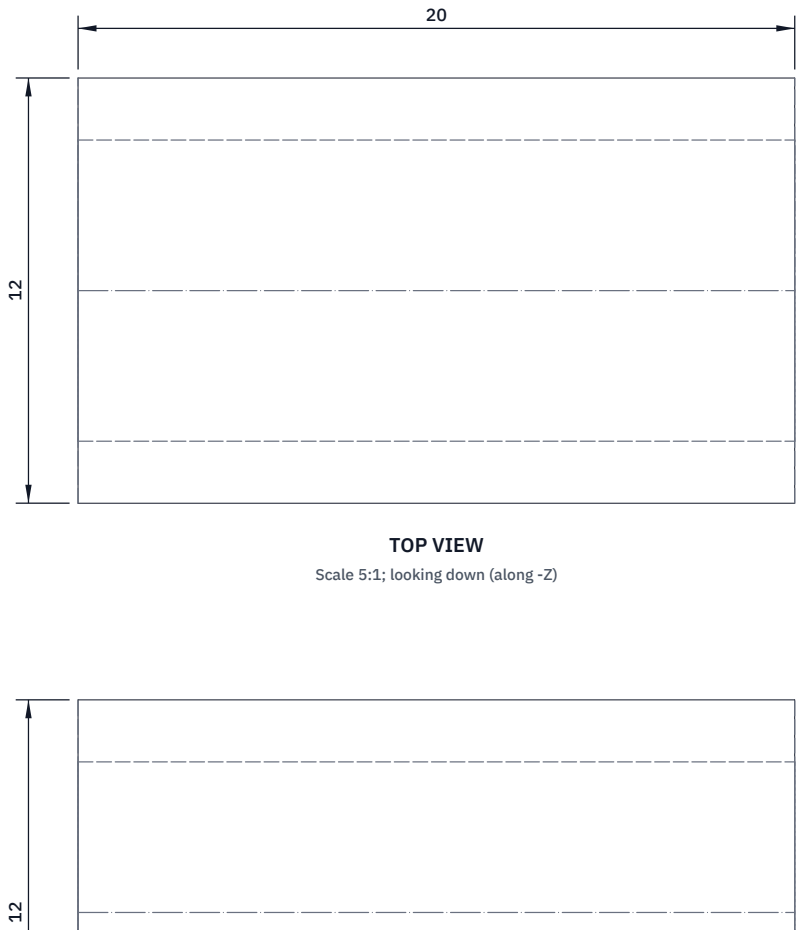
[picture p62: figure]
TOP VIEW; Scale 5:1; looking down (along -Z)

FRONT VIEW
Scale 5:1; looking at the front (along +Y)

RIGHT VIEW
Scale 5:1; looking at the right side (along -X)

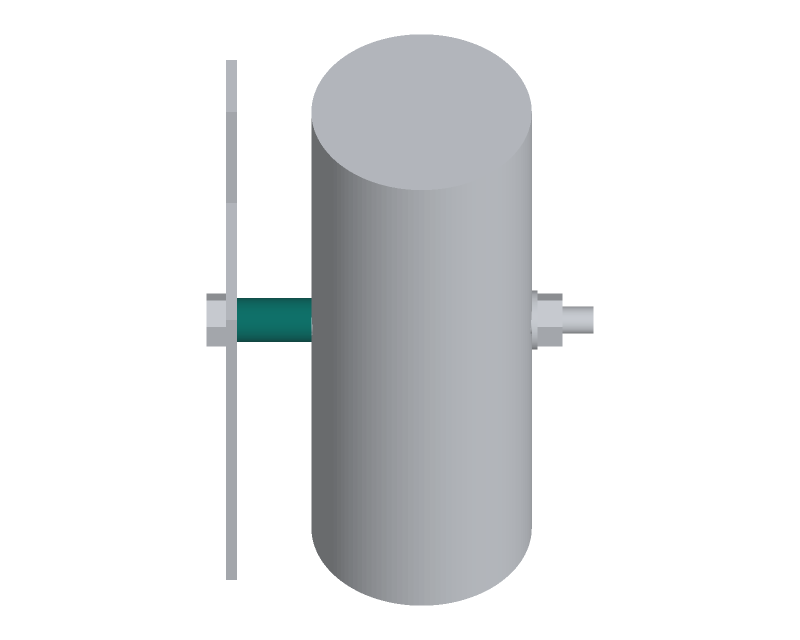
[picture p63: figure]

WHERE IT GOES
This part in colour, its neighbours in grey

HOW TO MAKE IT AND HOW IT FITS
Cut 20.2 mm of 12 mm aluminium tube (8.5 mm bore, or drill
the bore out to 8.5 mm). Face both ends square.
It fills the gap between the back of the bracket plate and the pole at the through-bolt, so tightening the bolt does not bend the plate. File the pole end to a shallow curve if it rocks on the pole.
Fit: on the M8 through-bolt between the plate and the pole. Check: length 20.2 mm, within 0.5 mm; on a 60 mm pole the plate stays flat when the bolt is tight.
REV | DESCRIPTION | DATE | BY
P1 | Making sketch for the prototype build plan | 2026-10-01 | AC
FLOODGAUGE | github.com/BoujeeEnjinia1701/floodgauge

## FloodGauge through-bolt spacer: making sketch

DRAWING NO.
FLG-DWG-109

REV
P1

SHEET
1 of 1

SIZE

## ANSI B

SCALE
5:1

UNITS
mm
PROJECTION | DATE
2026-10-01

DRAWN
Amish Chadha

MATERIAL / NOTES
Aluminium tube 12 mm OD, 8.5 mm bore
Licensed CERN-OHL-S-2.0 · Design Molecule Lab · designmolecule.com | Generated from cad/src; do not edit by hand
