BoujeeEnjinia1701/floodgauge/cad/drawings/FLG-DWG-112.pdf

BUILD PLAN SKETCH, PLAN NOT YET BUILT FloodGauge · github.com/BoujeeEnjinia1701/floodgauge

FRONT VIEW
Scale 1:10; looking at the front (along +Y)

TOP VIEW
Scale 1:10; looking down (along -Z)

RIGHT VIEW
Scale 1:10; looking at the right side (along -X)

75

75 940

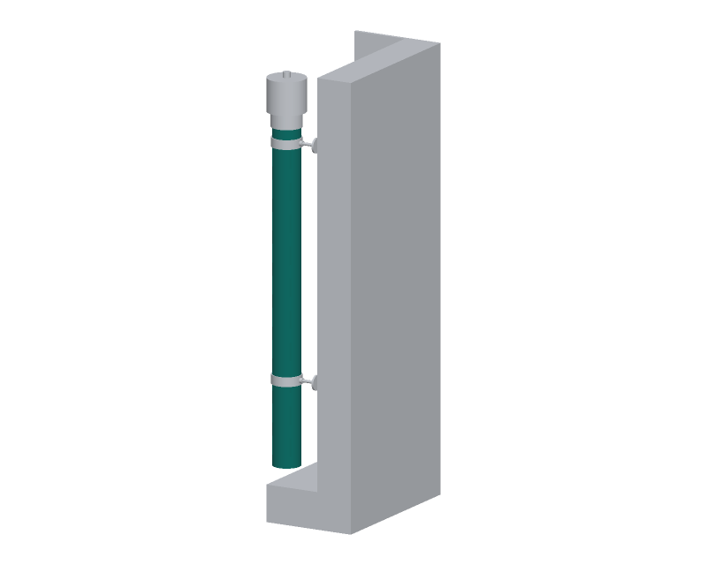
[picture p64: figure]

WHERE IT GOES
This part in colour, its neighbours in grey

HOW TO MAKE IT AND HOW IT FITS
Cut 940 mm of 75 mm PVC pipe; square and deburr both ends. Slots 5 x 50 mm: ten rows, four slots a row at 90 degrees apart. Row centres 55 mm from the bottom end, then every 85 mm.
Turn the slots 45 degrees off the line to the basin wall (where the clamp rods are). Cut with a hand saw and file, or a router.
Two 3.5 mm pilot holes 20 mm below the top end, one each side, for the screws that hold the drain head socket.
Mark the clamp positions: 80 and 710 mm below the top end.
Fit: hangs in the basin 90 mm from the curb-side wall on two stand-off pipe clamps; top end 300 mm below the road; the open bottom end 60 mm above the basin floor.
Check: a 50 mm ball dropped in falls straight out of the bottom.
REV | DESCRIPTION | DATE | BY
P1 | Making sketch for the prototype build plan | 2026-10-01 | AC
FLOODGAUGE | github.com/BoujeeEnjinia1701/floodgauge

## FloodGauge stilling tube: making sketch

DRAWING NO.
FLG-DWG-112

REV
P1

SHEET
1 of 1

SIZE

## ANSI B

SCALE
1:10

UNITS
mm
PROJECTION | DATE
2026-10-01

DRAWN
Amish Chadha

MATERIAL / NOTES
PVC pressure or drain pipe 75 mm OD, 3 mm wall
Licensed CERN-OHL-S-2.0 · Design Molecule Lab · designmolecule.com | Generated from cad/src; do not edit by hand
