BoujeeEnjinia1701/floodgauge/cad/drawings/FLG-DWG-113.pdf

BUILD PLAN SKETCH, PLAN NOT YET BUILT FloodGauge · github.com/BoujeeEnjinia1701/floodgauge

FRONT VIEW
Scale 1:2; looking at the front (along +Y)

TOP VIEW
Scale 1:2; looking down (along -Z)

RIGHT VIEW
Scale 1:2; looking at the right side (along -X)

104

104 145

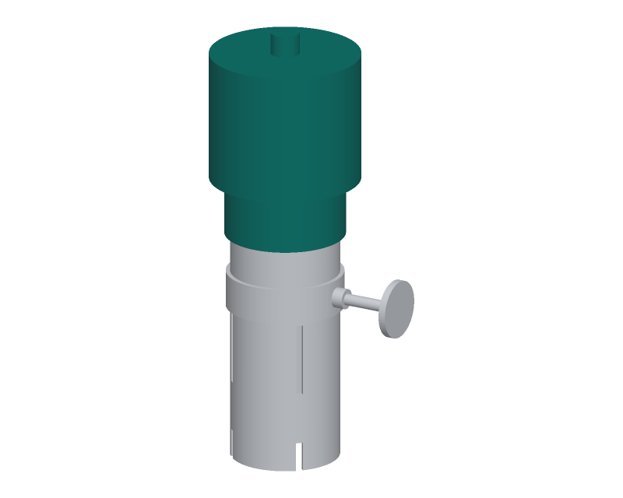
[picture p65: figure]

WHERE IT GOES
This part in colour, its neighbours in grey

HOW TO MAKE IT AND HOW IT FITS
Body: a sealed PVC cap about 104 mm across and 90 mm tall.
Socket: a 75 mm PVC socket coupling cut to 40 mm, solvent-welded under the body, centred. The tube top slides into it up to the body.
Inside: the ultrasonic ranger, transducer face down and flush with
the inside of the socket; the 10 k NTC beside it; two stainless wet
probe pins 10 mm below the face, 36 mm apart; a cable gland on top. Pot the electronics, keeping the transducer face and the probe tips clear of potting compound.
Fit: push over the tube top; two stainless screws through the socket into the tube's pilot holes. Undo them to lift the head for cleaning. Transducer face 300 mm below the road.
Check: the socket slides fully onto a tube offcut; probe tips clean.
REV | DESCRIPTION | DATE | BY
P1 | Making sketch for the prototype build plan | 2026-10-01 | AC
FLOODGAUGE | github.com/BoujeeEnjinia1701/floodgauge

## FloodGauge drain head: making sketch

DRAWING NO.
FLG-DWG-113

REV
P1

SHEET
1 of 1

SIZE

## ANSI B

SCALE
1:2

UNITS
mm
PROJECTION | DATE
2026-10-01

DRAWN
Amish Chadha

MATERIAL / NOTES
PVC cap 104 mm, 75 mm PVC socket, potting compound
Licensed CERN-OHL-S-2.0 · Design Molecule Lab · designmolecule.com | Generated from cad/src; do not edit by hand
