BoujeeEnjinia1701/floodgauge/media/card.png

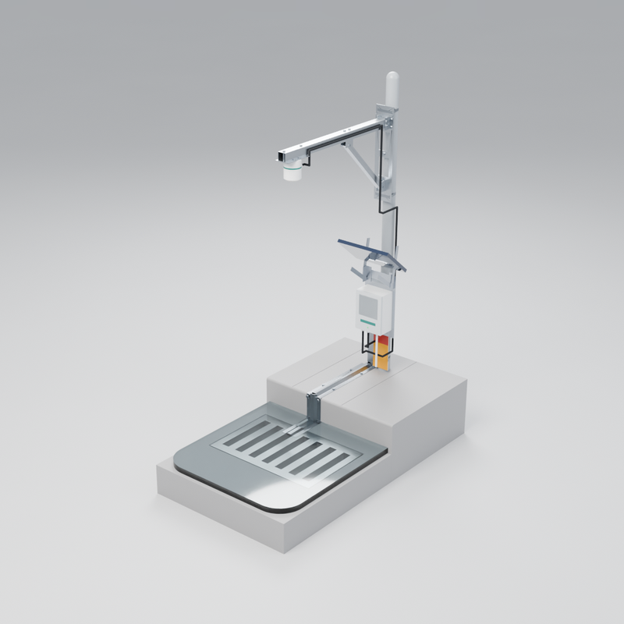
media/card.png
