BoujeeEnjinia1701/floodgauge/media/render-detail.png

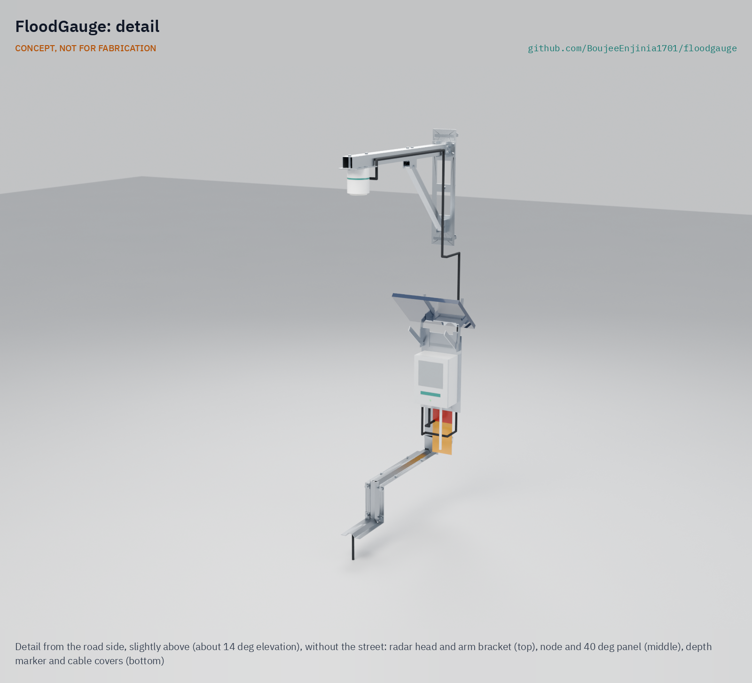
media/render-detail.png
