BoujeeEnjinia1701/floodgauge/media/render-exploded.png

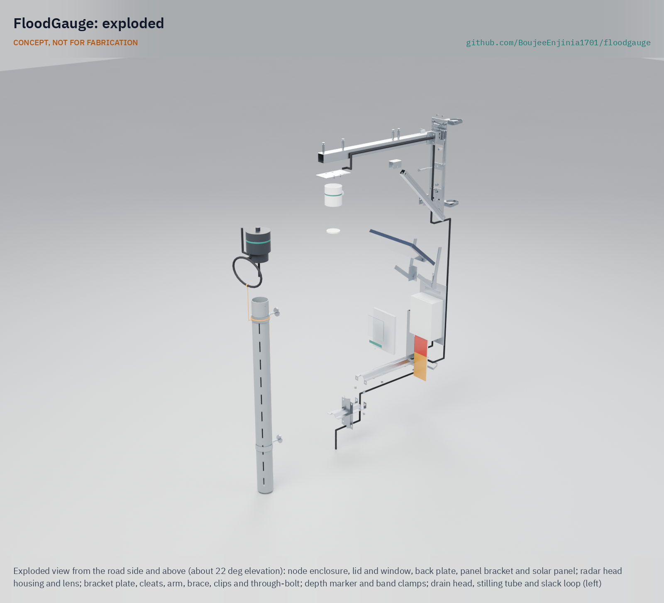
media/render-exploded.png
