BoujeeEnjinia1701/floodgauge/media/social-preview.png

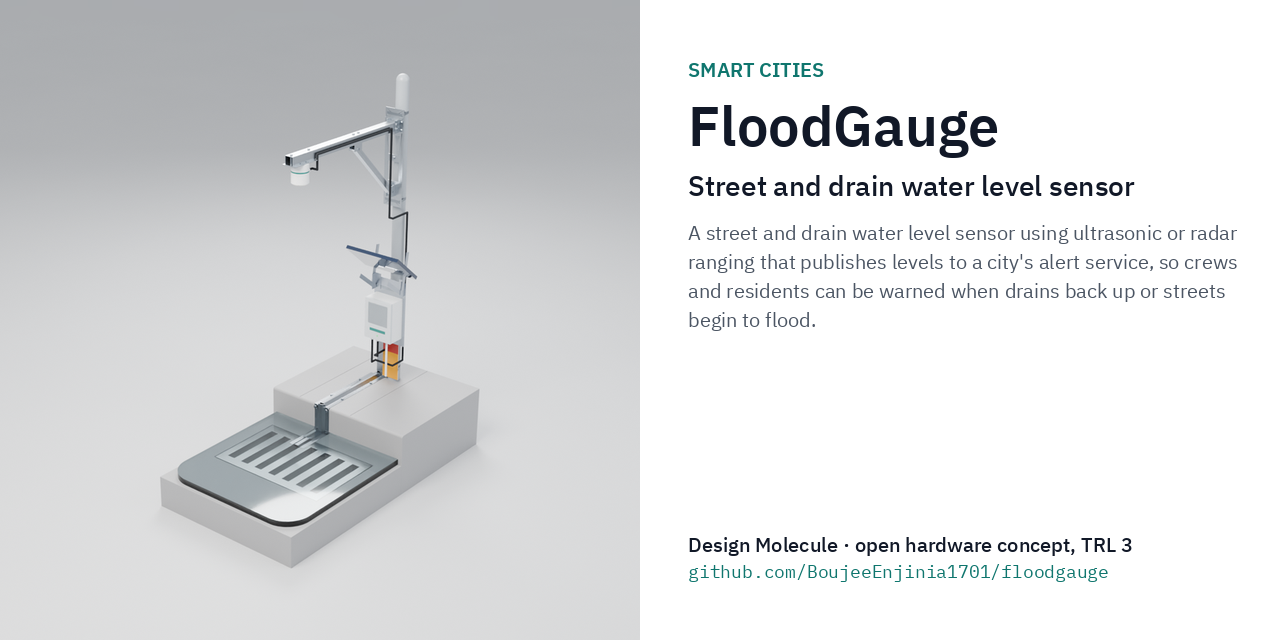
media/social-preview.png
